TheOriginalAndrobot/ada-dollhouse-controller/pictures/motherboard_bottom.png

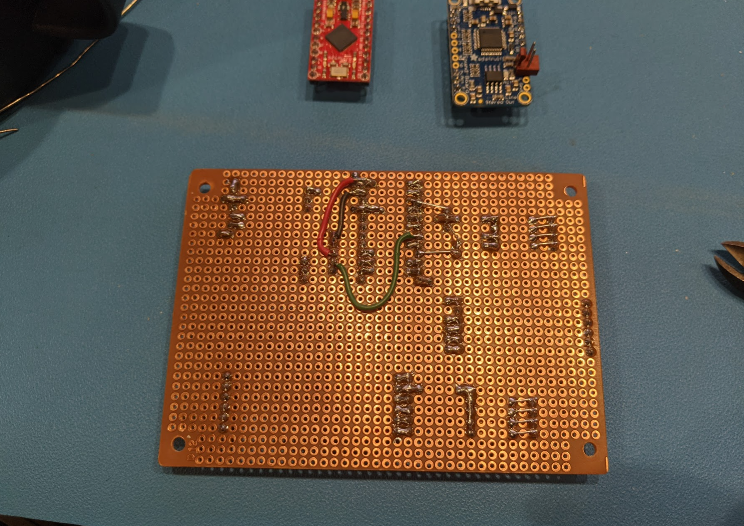
pictures/motherboard_bottom.png
